ReadAirCN/CW-Pocket-Trainer/Keil-Project/CW训练器工程-自动键版本/SRC/StdPeriphDriver/src/ch32f10x_flash.c

/********************************** (C) COPYRIGHT  *******************************
 * File Name          : ch32f10x_flash.c
 * Author             : WCH
 * Version            : V1.0.0
 * Date               : 2019/10/15
 * Description        : This file provides all the FLASH firmware functions.
*********************************************************************************
* Copyright (c) 2021 Nanjing Qinheng Microelectronics Co., Ltd.
* Attention: This software (modified or not) and binary are used for 
* microcontroller manufactured by Nanjing Qinheng Microelectronics.
*******************************************************************************/
#include "ch32f10x_flash.h"

/* Flash Access Control Register bits */
#define ACR_LATENCY_Mask         ((uint32_t)0x00000038)
#define ACR_HLFCYA_Mask          ((uint32_t)0xFFFFFFF7)
#define ACR_PRFTBE_Mask          ((uint32_t)0xFFFFFFEF)

/* Flash Access Control Register bits */
#define ACR_PRFTBS_Mask          ((uint32_t)0x00000020)

/* Flash Control Register bits */
#define CR_PG_Set                ((uint32_t)0x00000001)
#define CR_PG_Reset              ((uint32_t)0xFFFFFFFE)
#define CR_PER_Set               ((uint32_t)0x00000002)
#define CR_PER_Reset             ((uint32_t)0xFFFFFFFD)
#define CR_MER_Set               ((uint32_t)0x00000004)
#define CR_MER_Reset             ((uint32_t)0xFFFFFFFB)
#define CR_OPTPG_Set             ((uint32_t)0x00000010)
#define CR_OPTPG_Reset           ((uint32_t)0xFFFFFFEF)
#define CR_OPTER_Set             ((uint32_t)0x00000020)
#define CR_OPTER_Reset           ((uint32_t)0xFFFFFFDF)
#define CR_STRT_Set              ((uint32_t)0x00000040)
#define CR_LOCK_Set              ((uint32_t)0x00000080)
#define CR_FAST_LOCK_Set         ((uint32_t)0x00008000)
#define CR_PAGE_PG 	             ((uint32_t)0x00010000)
#define CR_PAGE_ER				       ((uint32_t)0x00020000)
#define CR_BUF_LOAD 	           ((uint32_t)0x00040000)
#define CR_BUF_RST 					     ((uint32_t)0x00080000)

/* FLASH Status Register bits */
#define SR_BSY 					         ((uint32_t)0x00000001)
#define SR_PGERR 					       ((uint32_t)0x00000004)
#define SR_WRPRTERR 					   ((uint32_t)0x00000010)
#define SR_EOP 					         ((uint32_t)0x00000020)

/* FLASH Mask */
#define RDPRT_Mask               ((uint32_t)0x00000002)
#define WRP0_Mask                ((uint32_t)0x000000FF)
#define WRP1_Mask                ((uint32_t)0x0000FF00)
#define WRP2_Mask                ((uint32_t)0x00FF0000)
#define WRP3_Mask                ((uint32_t)0xFF000000)
#define OB_USER_BFB2             ((uint16_t)0x0008)

/* FLASH Keys */
#define RDP_Key                  ((uint16_t)0x00A5)
#define FLASH_KEY1               ((uint32_t)0x45670123)
#define FLASH_KEY2               ((uint32_t)0xCDEF89AB)

/* FLASH BANK address */
#define FLASH_BANK1_END_ADDRESS  ((uint32_t)0x807FFFF)

/* Delay definition */
#define EraseTimeout             ((uint32_t)0x000B0000)
#define ProgramTimeout           ((uint32_t)0x00002000)
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
